DCentralTech/bitaxe401/doc/back.png

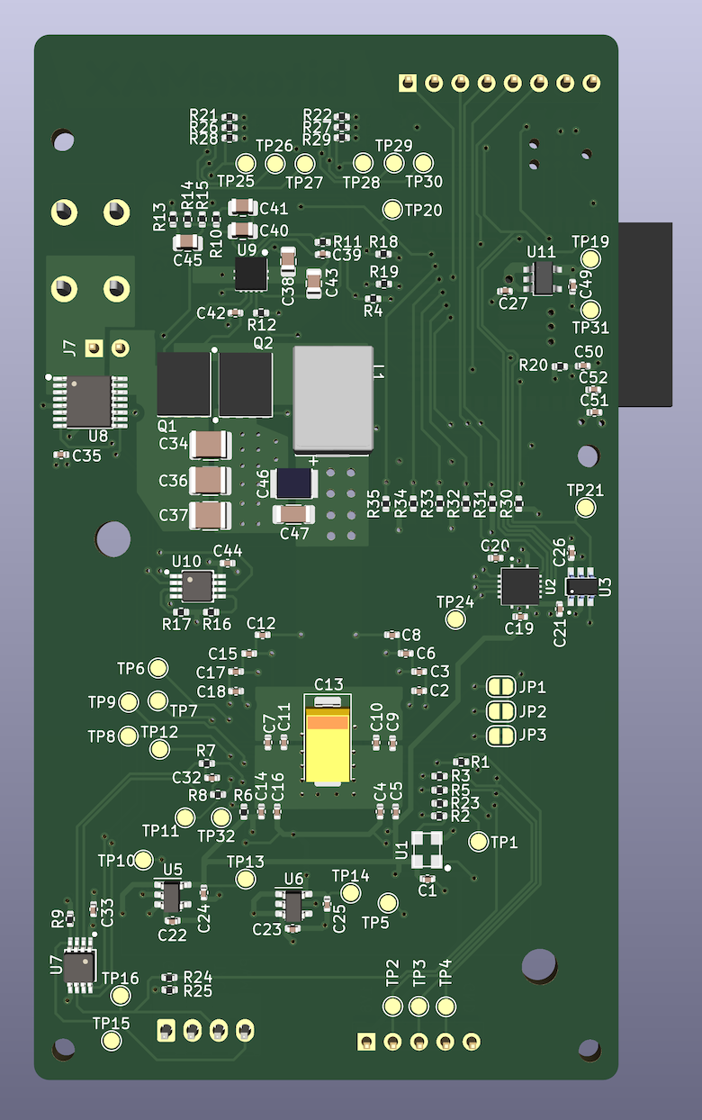
doc/back.png
