DCentralTech/bitaxe401/doc/bm1387.png

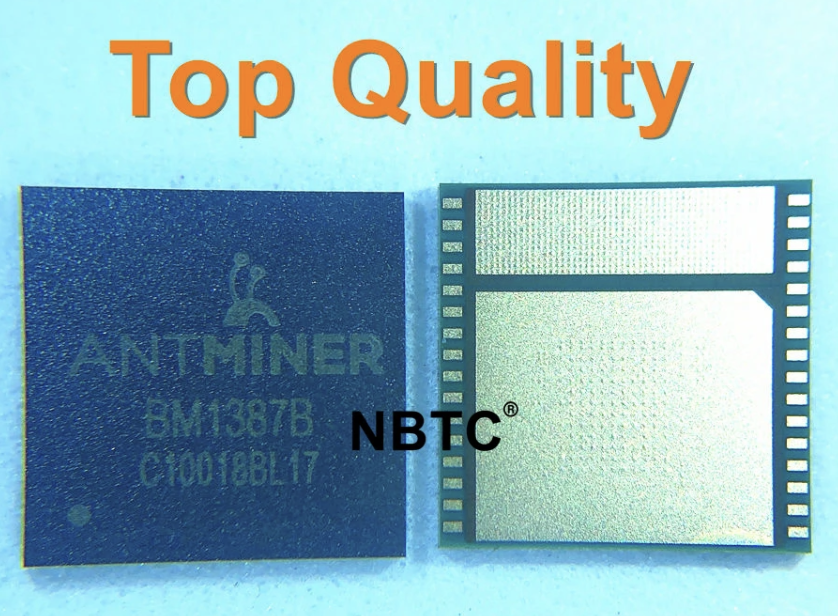
doc/bm1387.png
