DCentralTech/bitaxe401/doc/BM1397.png

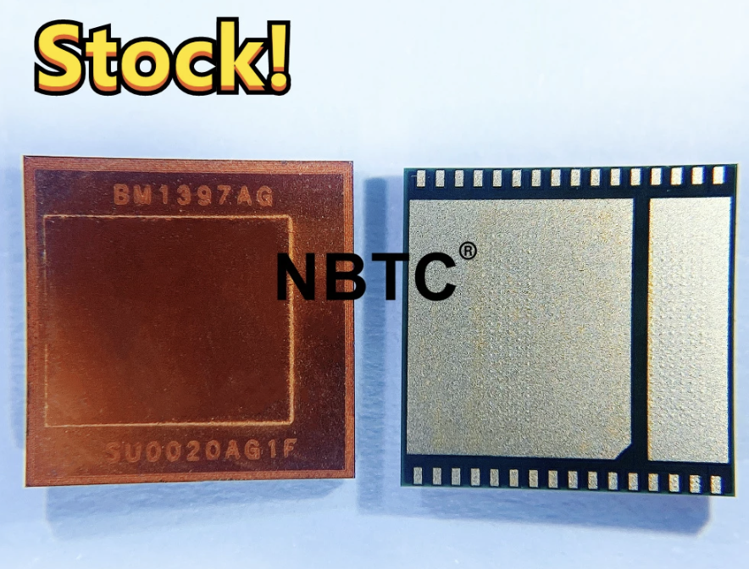
doc/BM1397.png
