DCentralTech/bitaxe401/doc/fan.png

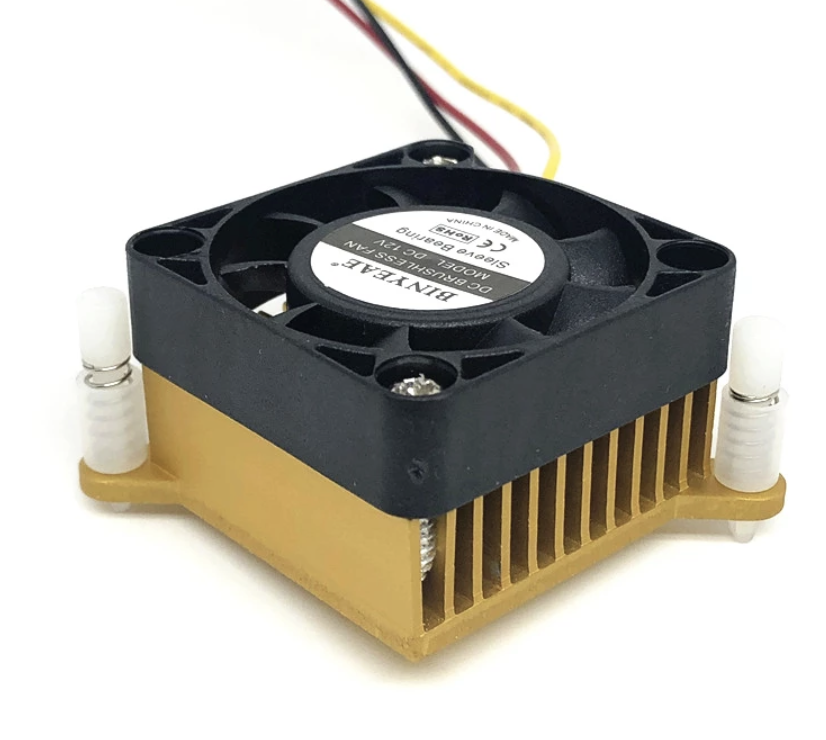
doc/fan.png
