DCentralTech/bitaxe401/3d/oscillator3.2x2.5.step

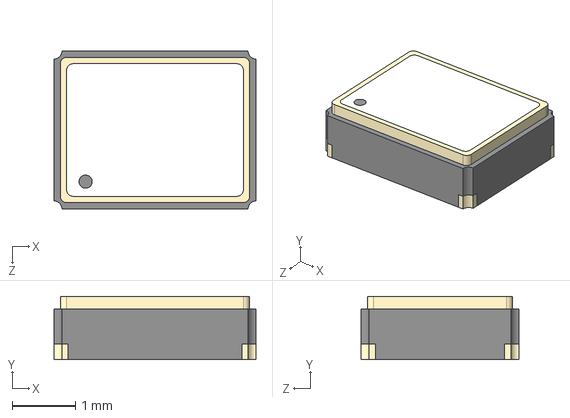
[picture p27: CAD file, 2024-08-15]
3d/oscillator3.2x2.5.step
3.20 x 1.00 x 2.50 mm
