DCentralTech/bitaxe401/3d/CS1213AG-tr.stp

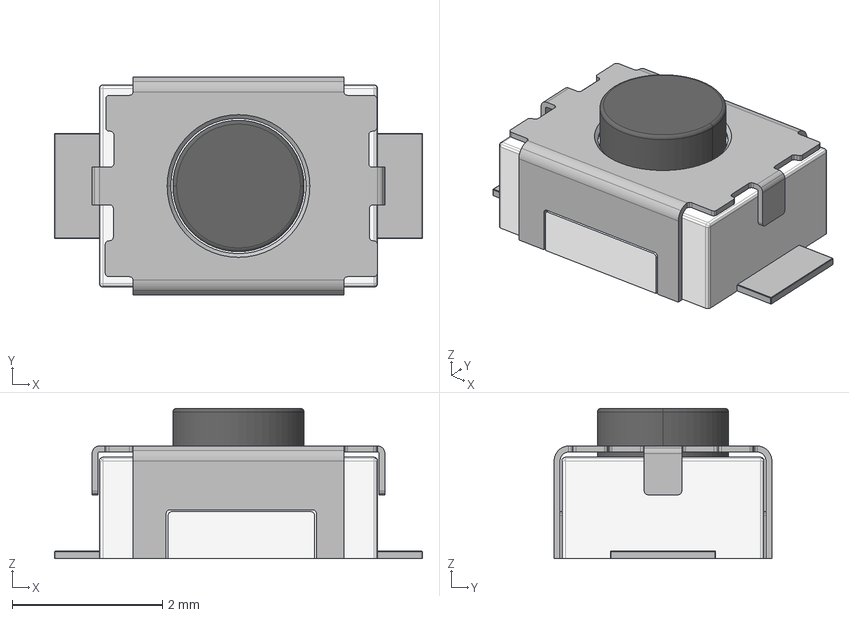
[picture p30: CAD file, 2024-08-15]
3d/CS1213AG-tr.stp
4.90 x 2.90 x 2.00 mm
