DCentralTech/bitaxe401/3d/CX3225SB16000H0FLJCC.STEP

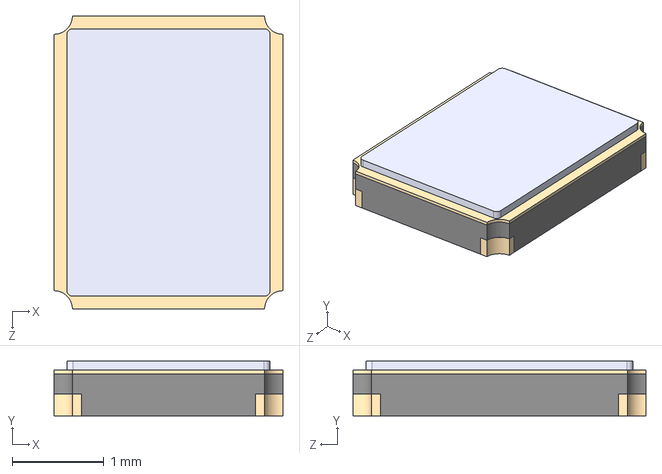
[picture p32: CAD file, 2024-08-15]
3d/CX3225SB16000H0FLJCC.STEP
2.50 x 0.6 x 3.20 mm
