DCentralTech/bitaxe401/3d/SN74AXC1T45DBVR.STEP

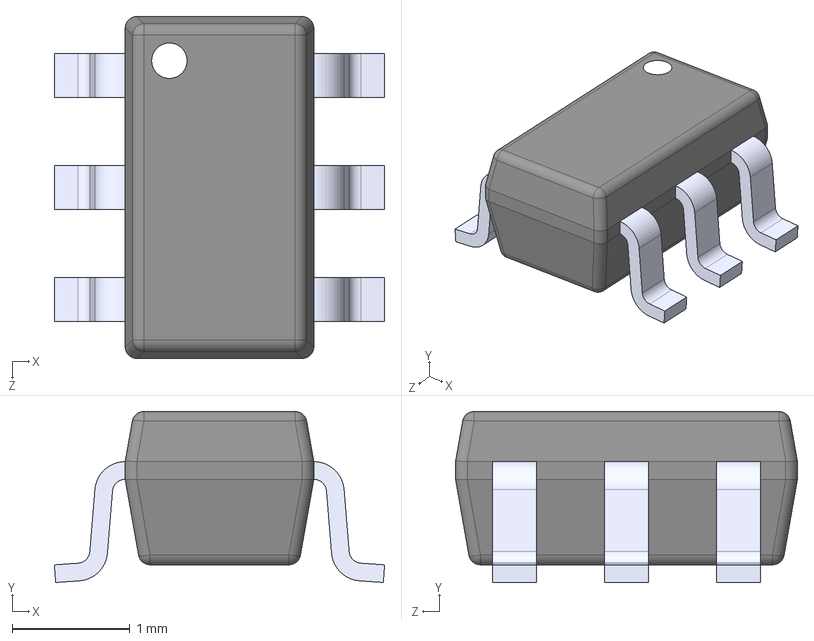
[picture p33: CAD file, 2024-08-15]
3d/SN74AXC1T45DBVR.STEP
2.80 x 1.45 x 2.90 mm
