DCentralTech/bitaxe401/3d/CUI_DEVICES_PJ-002AH.step

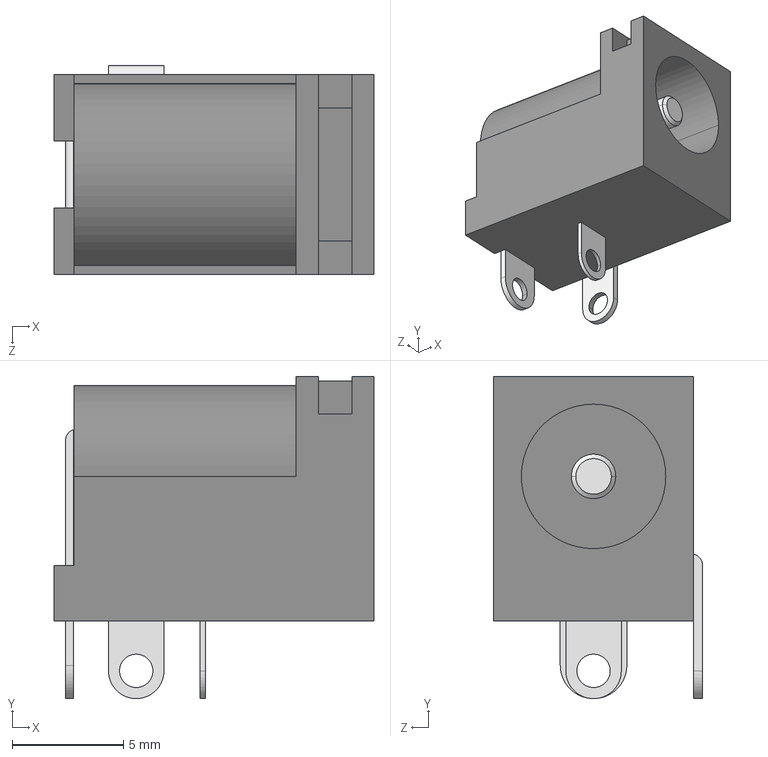
[picture p38: CAD file, 2024-08-15]
3d/CUI_DEVICES_PJ-002AH.step
14.4 x 14.5 x 9.40 mm
