DCentralTech/bitaxe401/3d/CUI_DEVICES_PJ-037AH.step

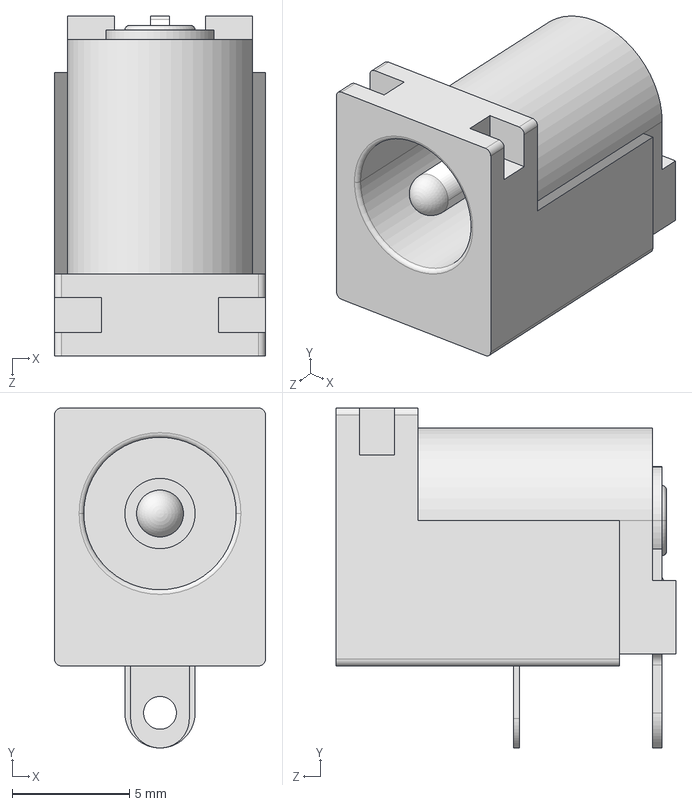
[picture p39: CAD file, 2024-08-15]
3d/CUI_DEVICES_PJ-037AH.step
9.00 x 14.5 x 14.5 mm
