DCentralTech/bitaxe401/3d/DRL0006A.stp

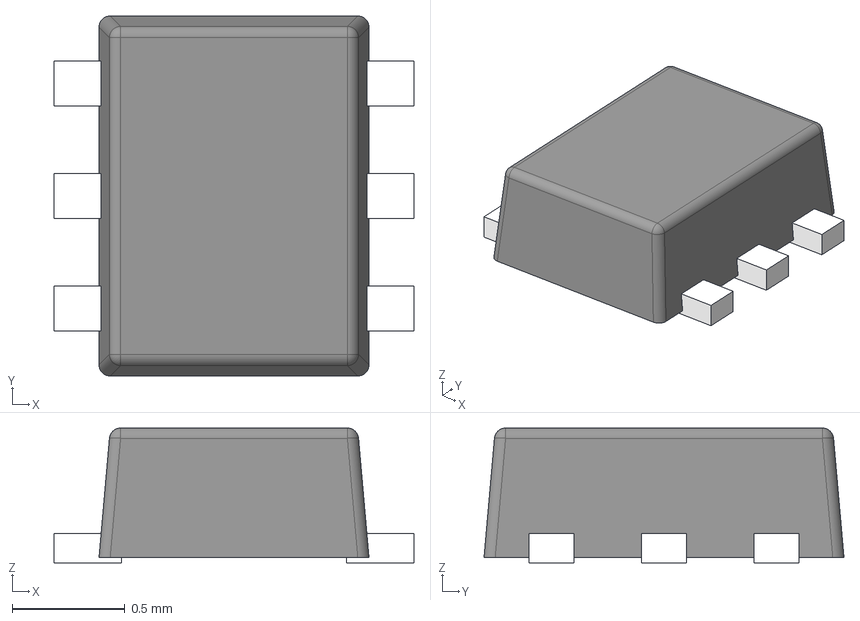
[picture p44: CAD file, 2024-08-15]
3d/DRL0006A.stp
1.60 x 1.60 x 0.6 mm
FRAME-DRL0006A
BODY-SOT
PIN1-ID
