DCentralTech/bitaxe401/3d/SW_CS1213AGF260_CRS.step

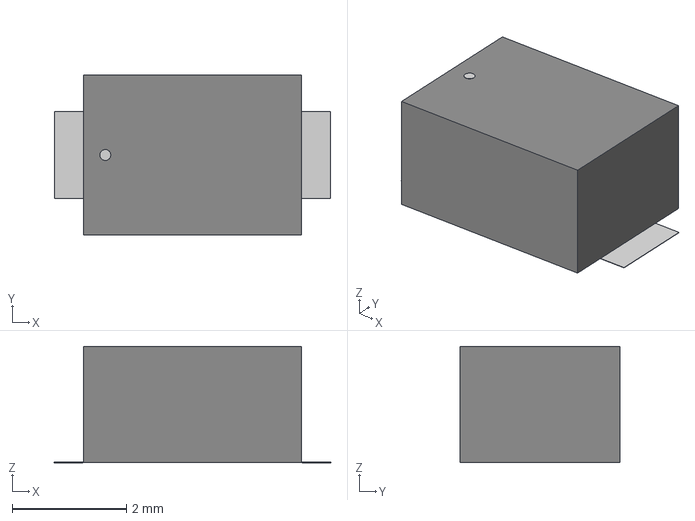
[picture p46: CAD file, 2024-08-15]
3d/SW_CS1213AGF260_CRS.step
4.83 x 2.79 x 2.04 mm
