DCentralTech/bitaxe401/3d/Bitaxe-Socket-Ice-Tower-Cooler-52pi-v1.2-4pins.step

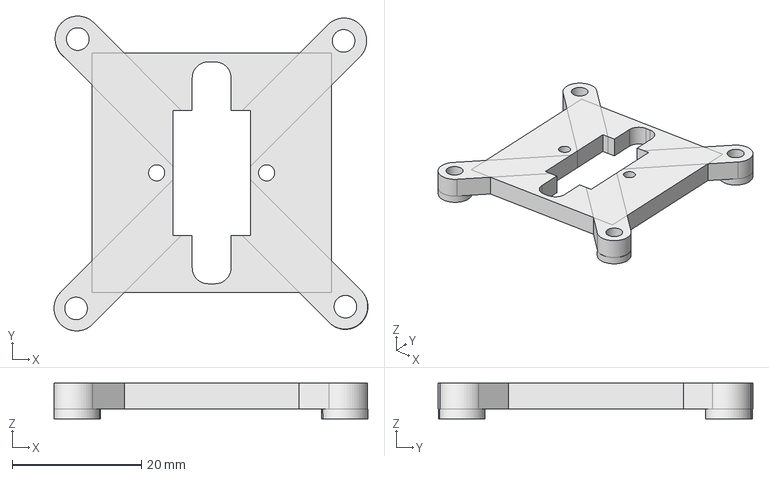
[picture p47: CAD file, 2024-08-15]
3d/Bitaxe-Socket-Ice-Tower-Cooler-52pi-v1.2-4pins.step
48.6 x 48.7 x 5.50 mm
